tudorz23/OpenBook_TSC/Images/pcb_3d_bottom.png

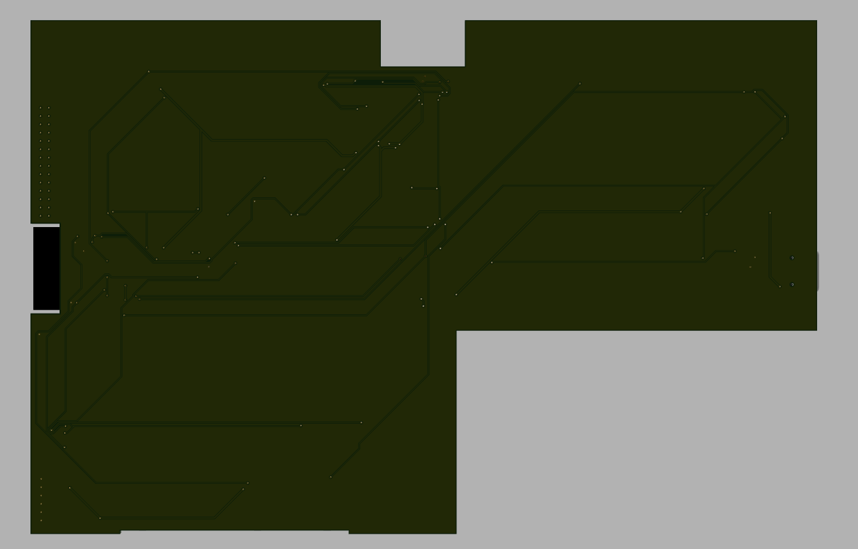
Images/pcb_3d_bottom.png
